instantdevices/USB-Killer-Detector/Project/V2/Pictures/Img_1.jpg

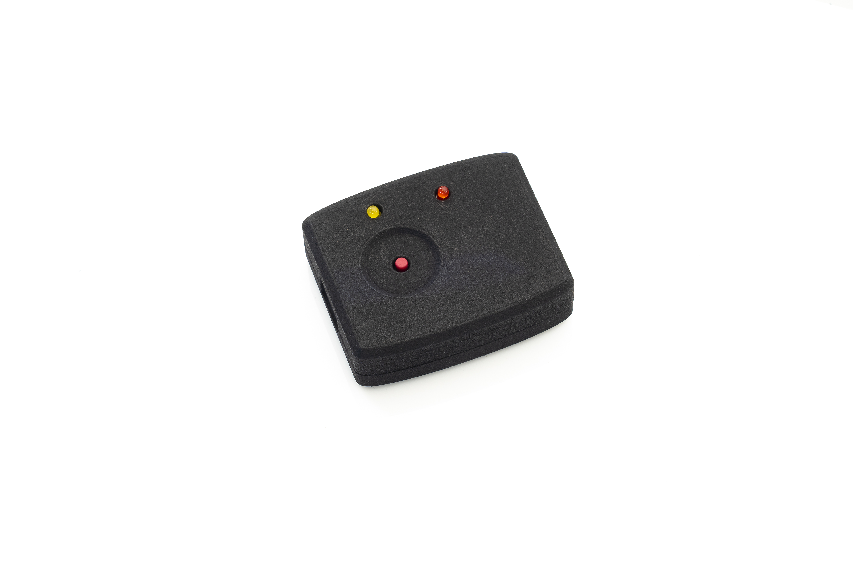
Project/V2/Pictures/Img_1.jpg
