instantdevices/USB-Killer-Detector/Project/V2/Pictures/Img_3.jpg

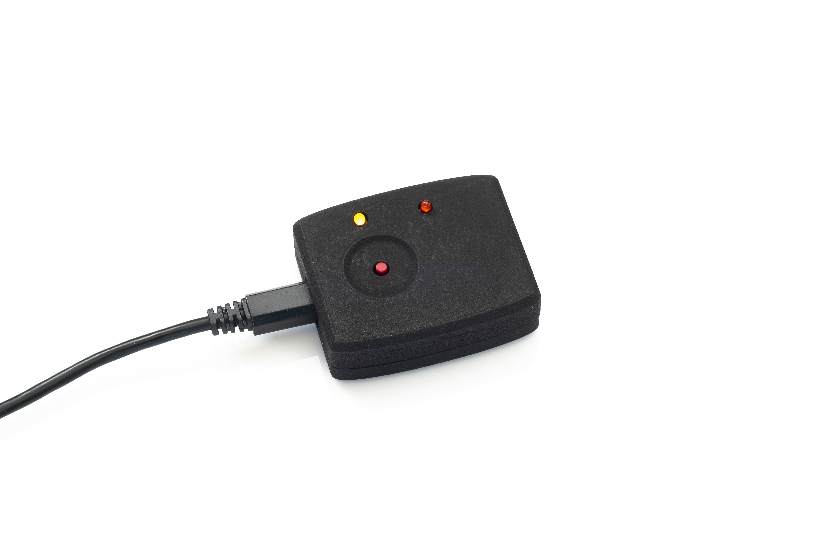
Project/V2/Pictures/Img_3.jpg
