instantdevices/USB-Killer-Detector/Project/V2/Pictures/Img_4.jpg

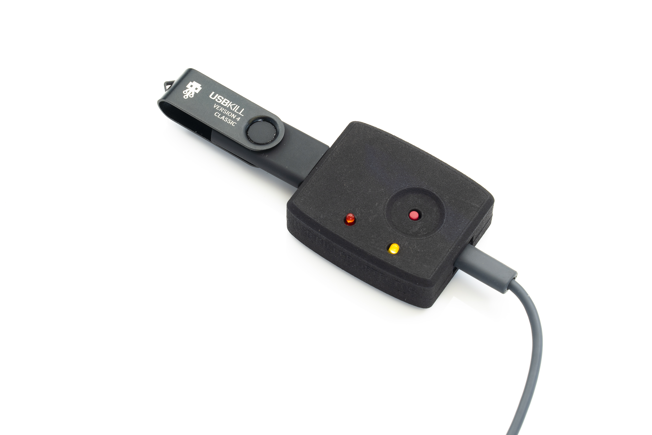
Project/V2/Pictures/Img_4.jpg
