instantdevices/USB-Killer-Detector/Project/V2/Pictures/Img_6.jpg

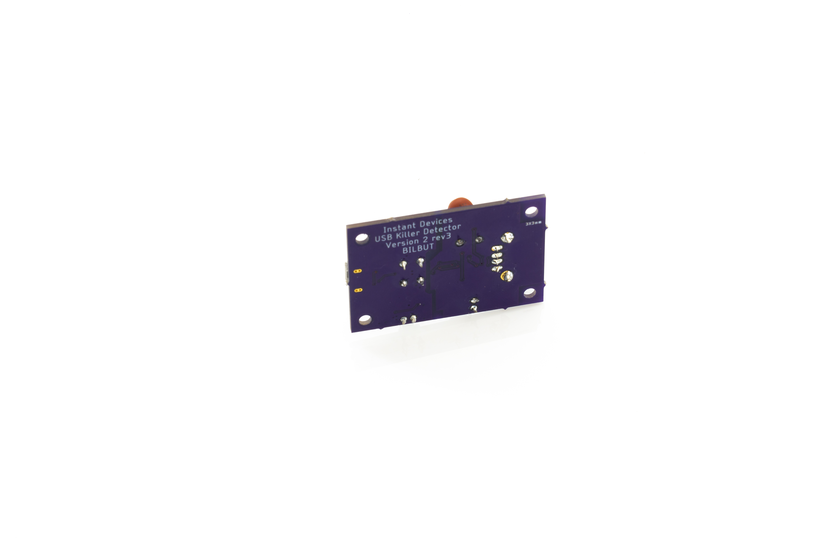
Project/V2/Pictures/Img_6.jpg
